jgromes/RadioShield/doc/revC/png/module_CC1101.png

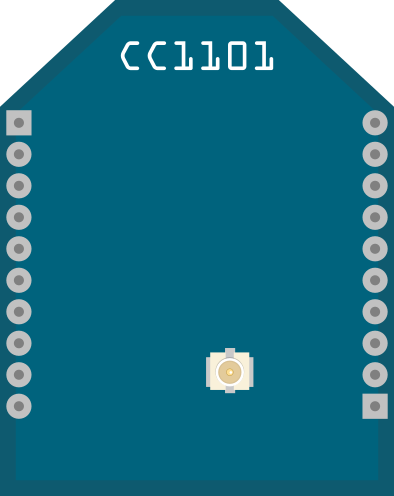
doc/revC/png/module_CC1101.png
