jgromes/RadioShield/doc/revC/png/module_HC05.png

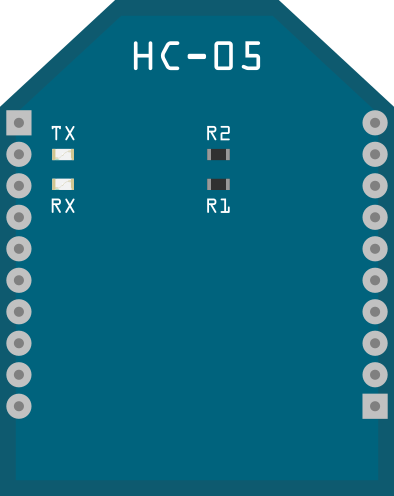
doc/revC/png/module_HC05.png
