jgromes/RadioShield/doc/revC/png/module_SX1272.png

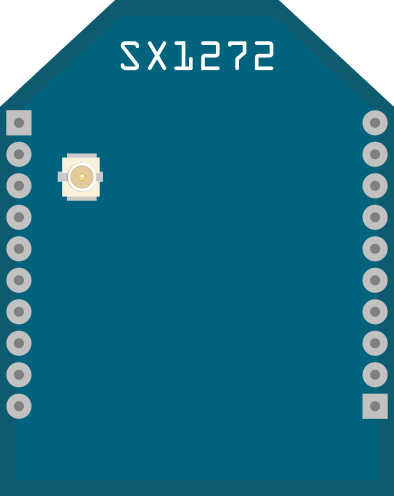
doc/revC/png/module_SX1272.png
