jgromes/RadioShield/eagle/revB/modules/module_ESP07.brd

## EAGLE design eagle/revB/modules/module_ESP07.brd (2018-07-29, an earlier design)

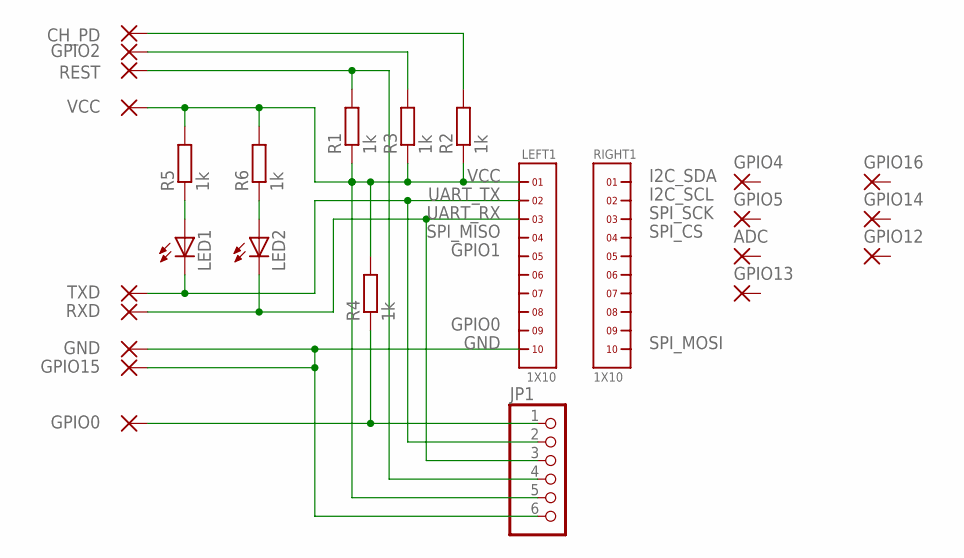
[picture p26: schematic module_ESP07.sch]

Parts:
ADC: WIREPADSMD1,27-254; SMD1,27-2,54
CH_PD: WIREPADSMD1,27-254; SMD1,27-2,54
GND: WIREPADSMD1,27-254; SMD1,27-2,54
GPIO0, GPIO2, GPIO4, GPIO5, GPIO12, GPIO13, GPIO14, GPIO15, GPIO16: WIREPADSMD1,27-254; SMD1,27-2,54
JP1: PINHD-1X6; 1X06
LED1, LED2: LEDCHIPLED_0603; CHIPLED_0603
LEFT1: 1X10
R1, R2, R3, R4, R5, R6: 1k; R0603
REST: WIREPADSMD1,27-254; SMD1,27-2,54
RIGHT1: 1X10
RXD: WIREPADSMD1,27-254; SMD1,27-2,54
TXD: WIREPADSMD1,27-254; SMD1,27-2,54
VCC: WIREPADSMD1,27-254; SMD1,27-2,54

Connections:
GND: GND.1, GPIO15.1, JP1.6, LEFT1.10
GPIO0: GPIO0.1, JP1.1, R4.1
unnamed: GPIO2.1, R3.2
unnamed: CH_PD.1, R2.2
unnamed: LED2.A, R6.1
unnamed: LED1.A, R5.1
RST: JP1.4, R1.2, REST.1
UART_RX: JP1.3, LED2.C, LEFT1.3, RXD.1
UART_TX: JP1.2, LED1.C, LEFT1.2, TXD.1
VCC: JP1.5, LEFT1.1, R1.1, R2.1, R3.1, R4.2, R5.2, R6.2, VCC.1

Notes on the sheet:
VCC
I2C_SDA
I2C_SCL
SPI_SCK
SPI_CS
SPI_MOSI
UART_TX
UART_RX
SPI_MISO
GPIO1
GPIO0
GND

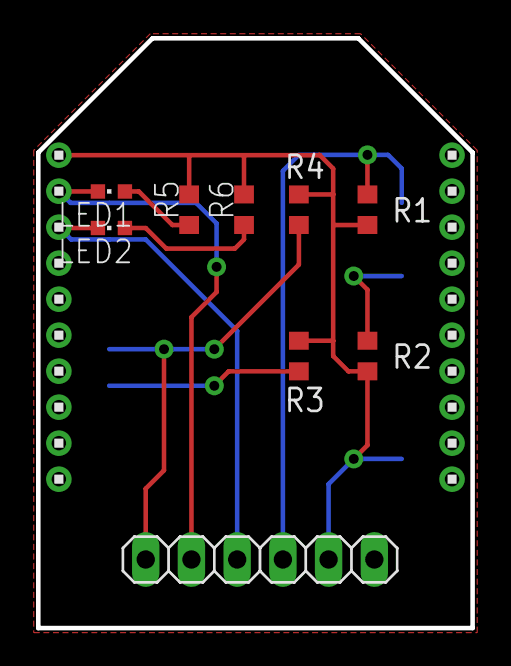
[picture p27: board eagle/revB/modules/module_ESP07.brd from above]

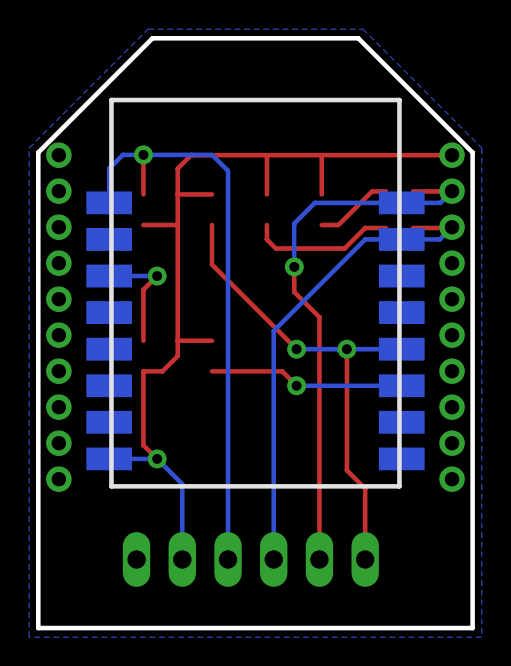
[picture p28: board eagle/revB/modules/module_ESP07.brd from below]

Board: 2 copper layers, 24.1 x 32.8 mm, 27 parts (16 on the bottom side), 10 nets.
