jgromes/RadioShield/eagle/revB/modules/module_HC05.brd

## EAGLE design eagle/revB/modules/module_HC05.brd (2018-07-17, an earlier design)

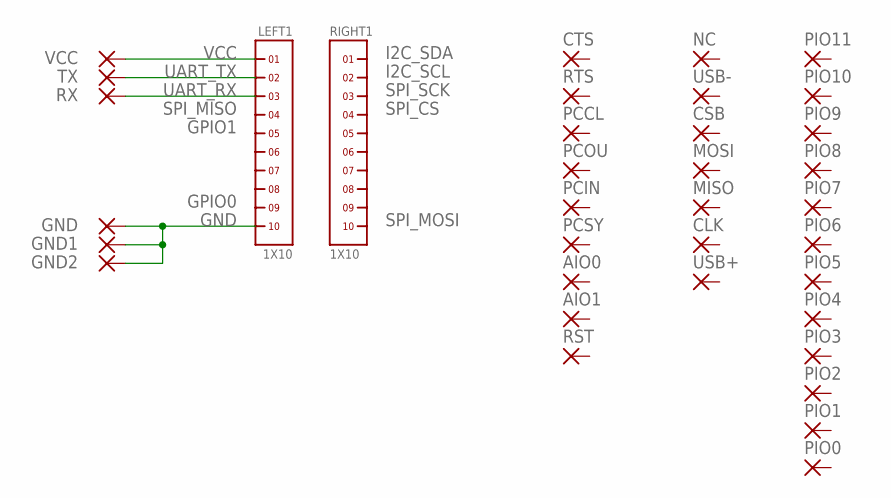
[picture p29: schematic module_HC05.sch]

Parts:
AIO0, AIO1: SMD1; SMD0,65-1,27
CLK: SMD1; SMD0,65-1,27
CSB: SMD1; SMD0,65-1,27
CTS: SMD1; SMD0,65-1,27
GND, GND1, GND2: SMD1; SMD0,65-1,27
LEFT1: 1X10
MISO: SMD1; SMD0,65-1,27
MOSI: SMD1; SMD0,65-1,27
NC: SMD1; SMD0,65-1,27
PCCL: SMD1; SMD0,65-1,27
PCIN: SMD1; SMD0,65-1,27
PCOU: SMD1; SMD0,65-1,27
PCSY: SMD1; SMD0,65-1,27
PIO0, PIO1, PIO2, PIO3, PIO4, PIO5, PIO6, PIO7, PIO8, PIO9, PIO10, PIO11: SMD1; SMD0,65-1,27
RIGHT1: 1X10
RST: SMD1; SMD0,65-1,27
RTS: SMD1; SMD0,65-1,27
RX: SMD1; SMD0,65-1,27
TX: SMD1; SMD0,65-1,27
USB+: SMD1; SMD0,65-1,27
USB-: SMD1; SMD0,65-1,27
VCC: SMD1; SMD0,65-1,27

Connections:
GND: GND.1, GND1.1, GND2.1, LEFT1.10
UART_RX: LEFT1.3, RX.1
UART_TX: LEFT1.2, TX.1
VCC: LEFT1.1, VCC.1

Notes on the sheet:
VCC
I2C_SDA
I2C_SCL
SPI_SCK
SPI_CS
SPI_MOSI
UART_TX
UART_RX
SPI_MISO
GPIO1
GPIO0
GND
