jgromes/RadioShield/eagle/revB/modules/module_HC05.brd

## EAGLE design eagle/revB/modules/module_HC05.brd (continued)

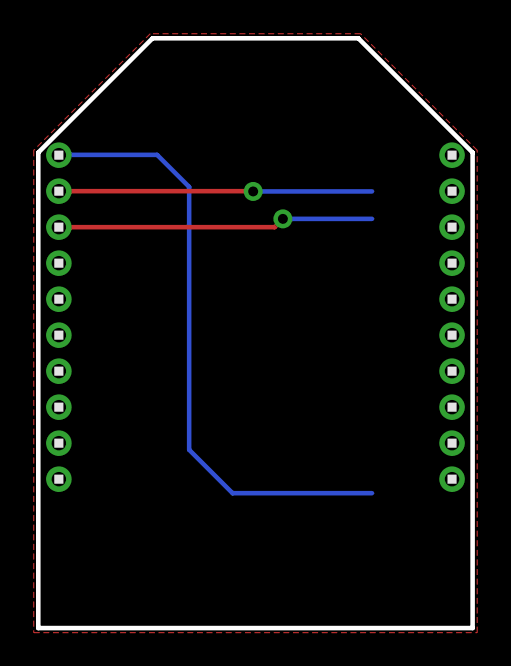
[picture p30: board eagle/revB/modules/module_HC05.brd from above]

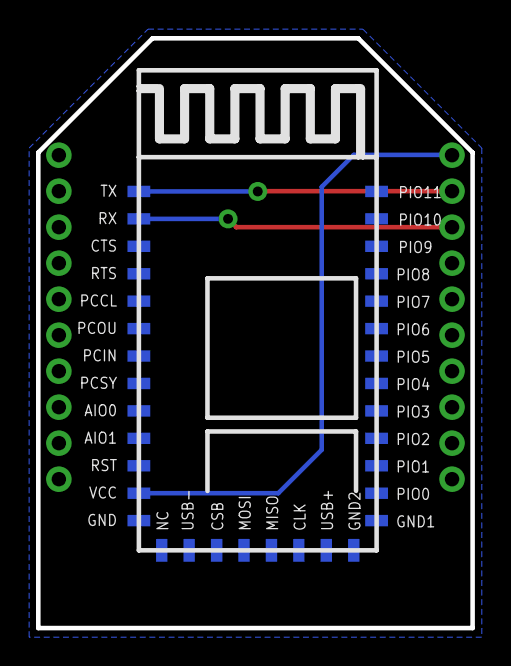
[picture p31: board eagle/revB/modules/module_HC05.brd from below]

Board: 2 copper layers, 24.1 x 32.8 mm, 36 parts (34 on the bottom side), 4 nets.
