jgromes/RadioShield/eagle/revB/shield.brd

## EAGLE design eagle/revB/shield.brd (2018-07-17, an earlier design)

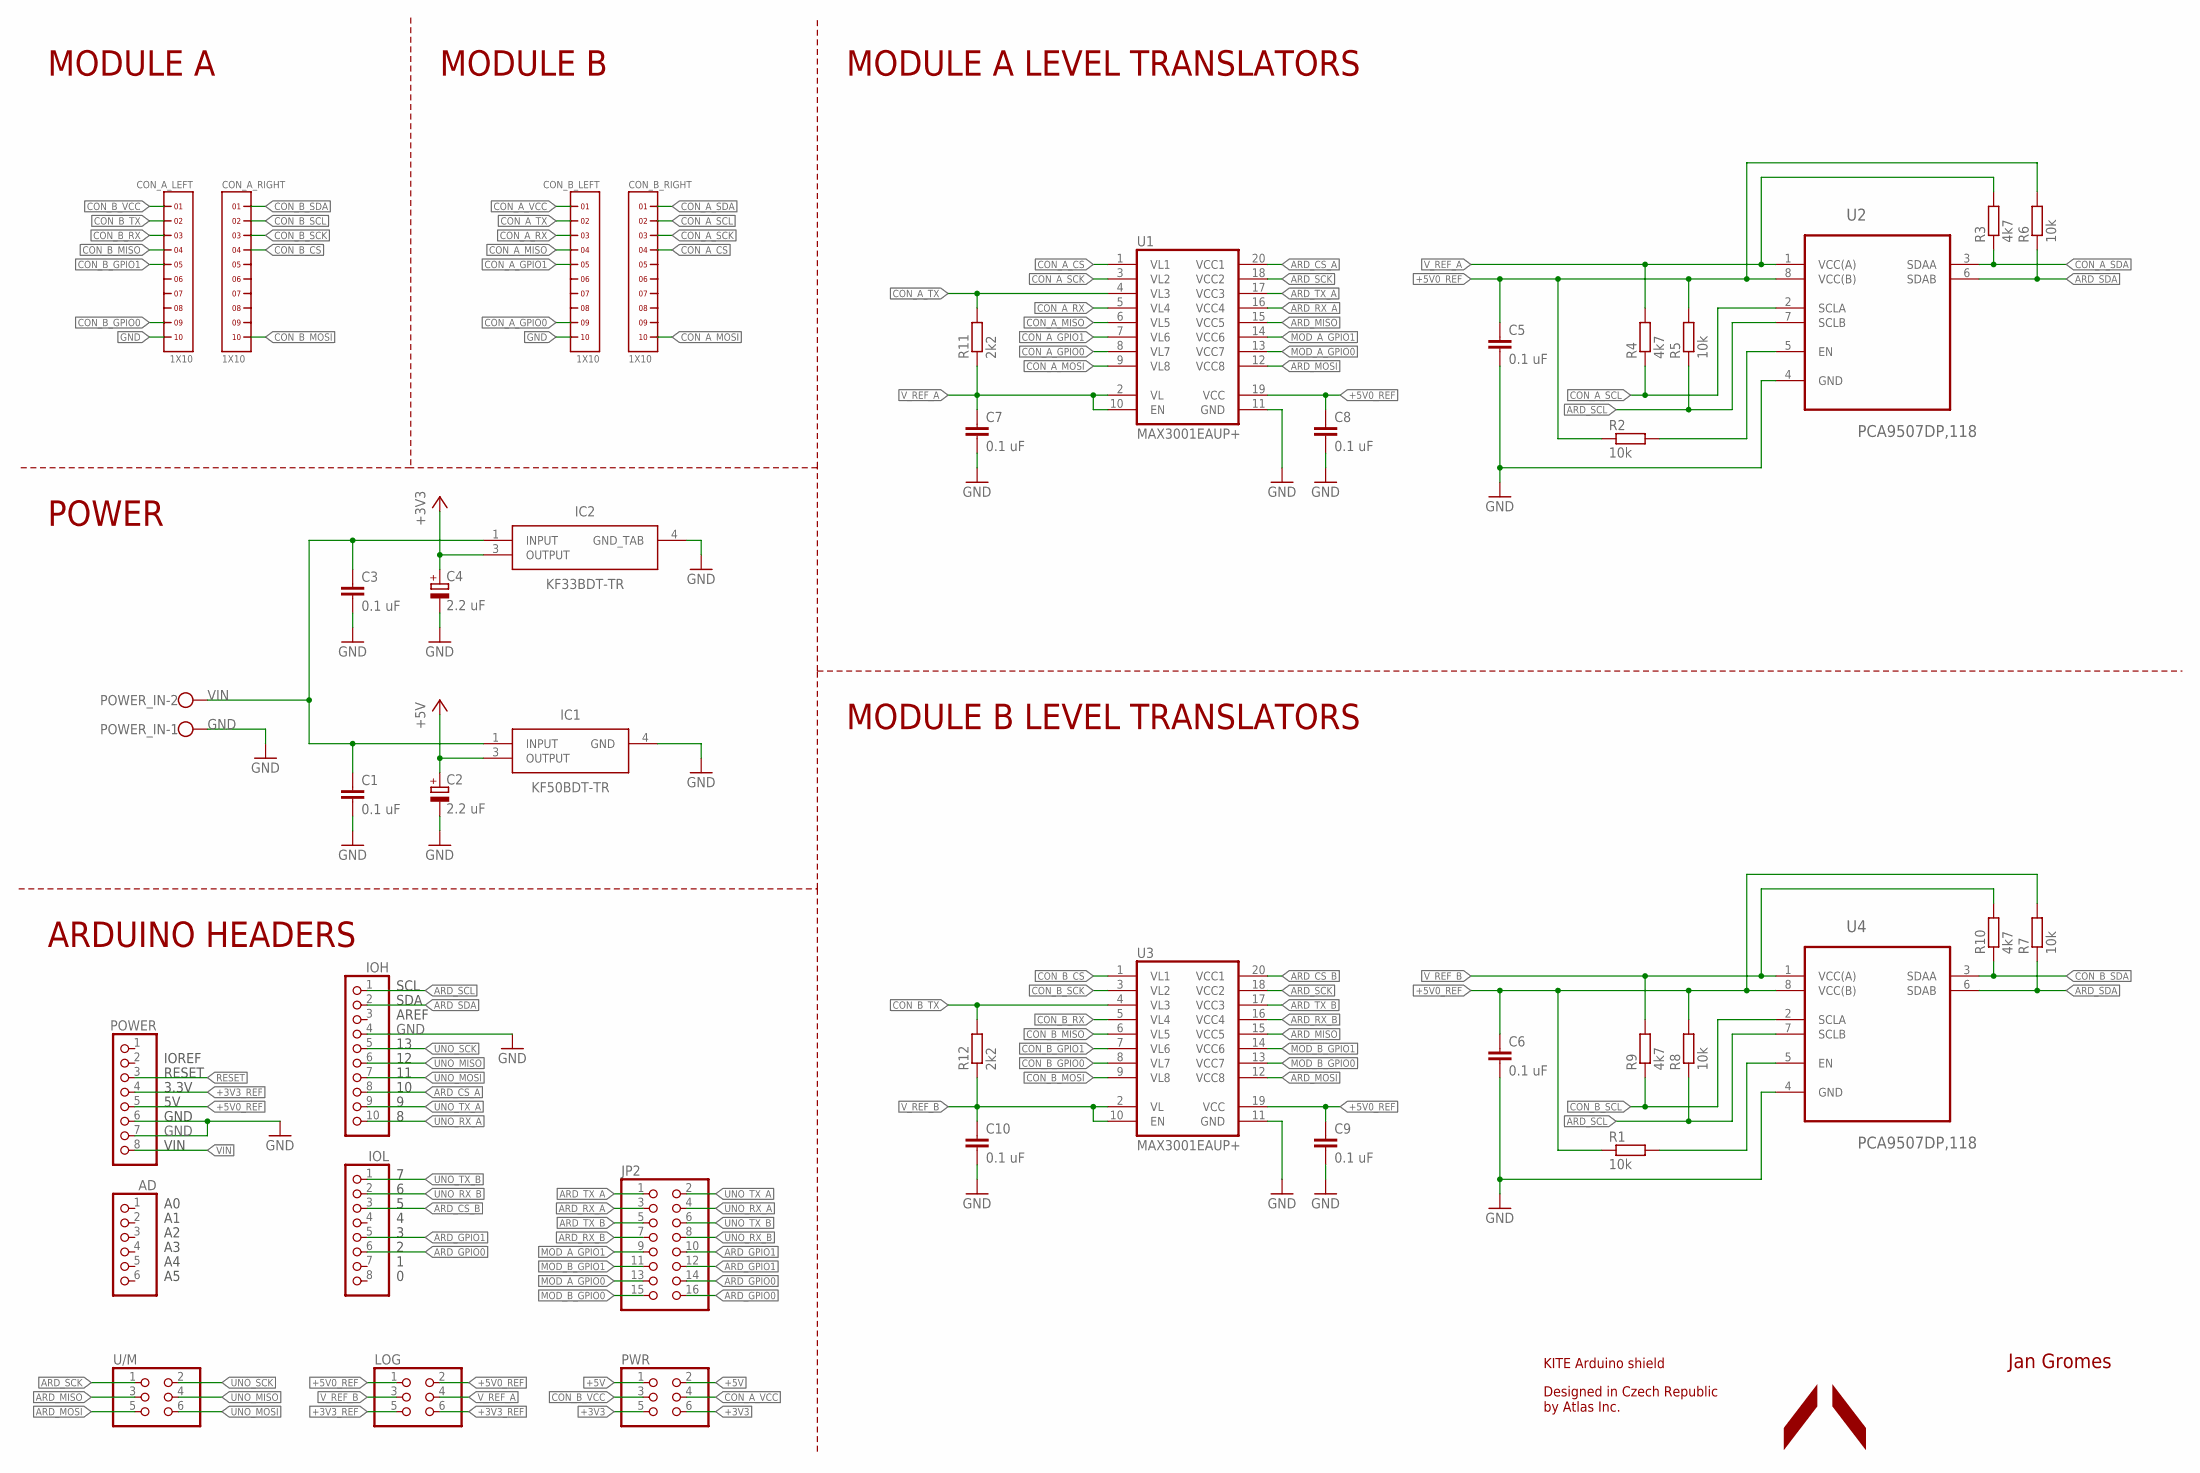
[picture p32: schematic shield.sch, Project WaveLength Arduino shield]

Parts:
AD: PINHD-1X6; 1X06
C1, C3, C5, C6, C7, C8, C9, C10: 0.1 uF; C0603
C2, C4: 2.2 uF; SMC_A
CON_A_LEFT: 1X10
CON_A_RIGHT: 1X10
CON_B_LEFT: 1X10
CON_B_RIGHT: 1X10
IC1: KF50BDT-TR; TO228P972X240-3N
IC2: KF33BDT-TR; TO228P972X240-3N
IOH: PINHD-1X10; 1X10
IOL: PINHD-1X8; 1X08
JP2: PINHD-2X8; 2X08
LOG: PINHD-2X3; 2X03
POWER: PINHD-1X8; 1X08
POWER_IN: W237-102
PWR: PINHD-2X3; 2X03
R1, R2, R5, R6, R7, R8: 10k; R0603
R3, R4, R9, R10: 4k7; R0603
R11, R12: 2k2; R0603
U1, U3: MAX3001EAUP+; TSSOP20
U2, U4: PCA9507DP,118; SOP65P490X110-8N
U/M: PINHD-2X3; 2X03

Connections:
+3V3: C4.+, IC2.3 (OUTPUT), PWR.5, PWR.6
+3V3_REF: LOG.5, LOG.6, POWER.4
+5V: C2.+, IC1.3 (OUTPUT), PWR.1, PWR.2
+5V0_REF: C5.1, C6.1, C8.1, C9.1, LOG.1, LOG.2, POWER.5, R1.1, R2.1, R5.2, R6.2, R7.2, R8.2, U1.19 (VCC), U2.8 (VCC(B)), U3.19 (VCC), U4.8 (VCC(B))
ARD_CS_A: IOH.8, U1.20 (VCC1)
ARD_CS_B: IOL.3, U3.20 (VCC1)
ARD_GPIO0: IOL.6, JP2.14, JP2.16
ARD_GPIO1: IOL.5, JP2.10, JP2.12
ARD_MISO: U1.15 (VCC5), U3.15 (VCC5), U/M.3
ARD_MOSI: U1.12 (VCC8), U3.12 (VCC8), U/M.5
ARD_RX_A: JP2.3, U1.16 (VCC4)
ARD_RX_B: JP2.7, U3.16 (VCC4)
ARD_SCK: U1.18 (VCC2), U3.18 (VCC2), U/M.1
ARD_SCL: IOH.1, R5.1, R8.1, U2.7 (SCLB), U4.7 (SCLB)
ARD_SDA: IOH.2, R6.1, R7.1, U2.6 (SDAB), U4.6 (SDAB)
ARD_TX_A: JP2.1, U1.17 (VCC3)
ARD_TX_B: JP2.5, U3.17 (VCC3)
CON_A_CS: CON_B_RIGHT.4, U1.1 (VL1)
CON_A_GPIO0: CON_B_LEFT.9, U1.8 (VL7)
CON_A_GPIO1: CON_B_LEFT.5, U1.7 (VL6)
CON_A_MISO: CON_B_LEFT.4, U1.6 (VL5)
CON_A_MOSI: CON_B_RIGHT.10, U1.9 (VL8)
CON_A_RX: CON_B_LEFT.3, U1.5 (VL4)
CON_A_SCK: CON_B_RIGHT.3, U1.3 (VL2)
CON_A_SCL: CON_B_RIGHT.2, R4.1, U2.2 (SCLA)
CON_A_SDA: CON_B_RIGHT.1, R3.1, U2.3 (SDAA)
CON_A_TX: CON_B_LEFT.2, R11.2, U1.4 (VL3)
CON_A_VCC: CON_B_LEFT.1, PWR.4
CON_B_CS: CON_A_RIGHT.4, U3.1 (VL1)
CON_B_GPIO0: CON_A_LEFT.9, U3.8 (VL7)
CON_B_GPIO1: CON_A_LEFT.5, U3.7 (VL6)
CON_B_MISO: CON_A_LEFT.4, U3.6 (VL5)
CON_B_MOSI: CON_A_RIGHT.10, U3.9 (VL8)
CON_B_RX: CON_A_LEFT.3, U3.5 (VL4)
CON_B_SCK: CON_A_RIGHT.3, U3.3 (VL2)
CON_B_SCL: CON_A_RIGHT.2, R9.1, U4.2 (SCLA)
CON_B_SDA: CON_A_RIGHT.1, R10.1, U4.3 (SDAA)
CON_B_TX: CON_A_LEFT.2, R12.2, U3.4 (VL3)
CON_B_VCC: CON_A_LEFT.1, PWR.3
GND: C1.2, C2.-, C3.2, C4.-, C5.2, C6.2, C7.2, C8.2, C9.2, C10.2, CON_A_LEFT.10, CON_B_LEFT.10, IC1.4 (GND), IC2.4 (GND_TAB), IOH.4, POWER.6, POWER.7, POWER_IN.1, U1.11 (GND), U2.4 (GND), U3.11 (GND), U4.4 (GND)
MOD_A_GPIO0: JP2.13, U1.13 (VCC7)
MOD_A_GPIO1: JP2.9, U1.14 (VCC6)
MOD_B_GPIO0: JP2.15, U3.13 (VCC7)
MOD_B_GPIO1: JP2.11, U3.14 (VCC6)
unnamed: R2.2, U2.5 (EN)
unnamed: R1.2, U4.5 (EN)
RESET: POWER.3
UNO_MISO: IOH.6, U/M.4
UNO_MOSI: IOH.7, U/M.6
UNO_RX_A: IOH.10, JP2.4
UNO_RX_B: IOL.2, JP2.8
UNO_SCK: IOH.5, U/M.2
UNO_TX_A: IOH.9, JP2.2
UNO_TX_B: IOL.1, JP2.6
VIN: C1.1, C3.1, IC1.1 (INPUT), IC2.1 (INPUT), POWER.8, POWER_IN.2
V_REF_A: C7.1, LOG.4, R3.2, R4.2, R11.1, U1.2 (VL), U1.10 (EN), U2.1 (VCC(A))
V_REF_B: C10.1, LOG.3, R9.2, R10.2, R12.1, U3.2 (VL), U3.10 (EN), U4.1 (VCC(A))

Notes on the sheet:
Jan Gromes
AREF
SDA
SCL
VIN
GND
3.3V
RESET
IOREF
MODULE B LEVEL TRANSLATORS
MODULE A LEVEL TRANSLATORS
MODULE A
MODULE B
POWER
ARDUINO HEADERS
KITE Arduino shield
Designed in Czech Republic by Atlas Inc.

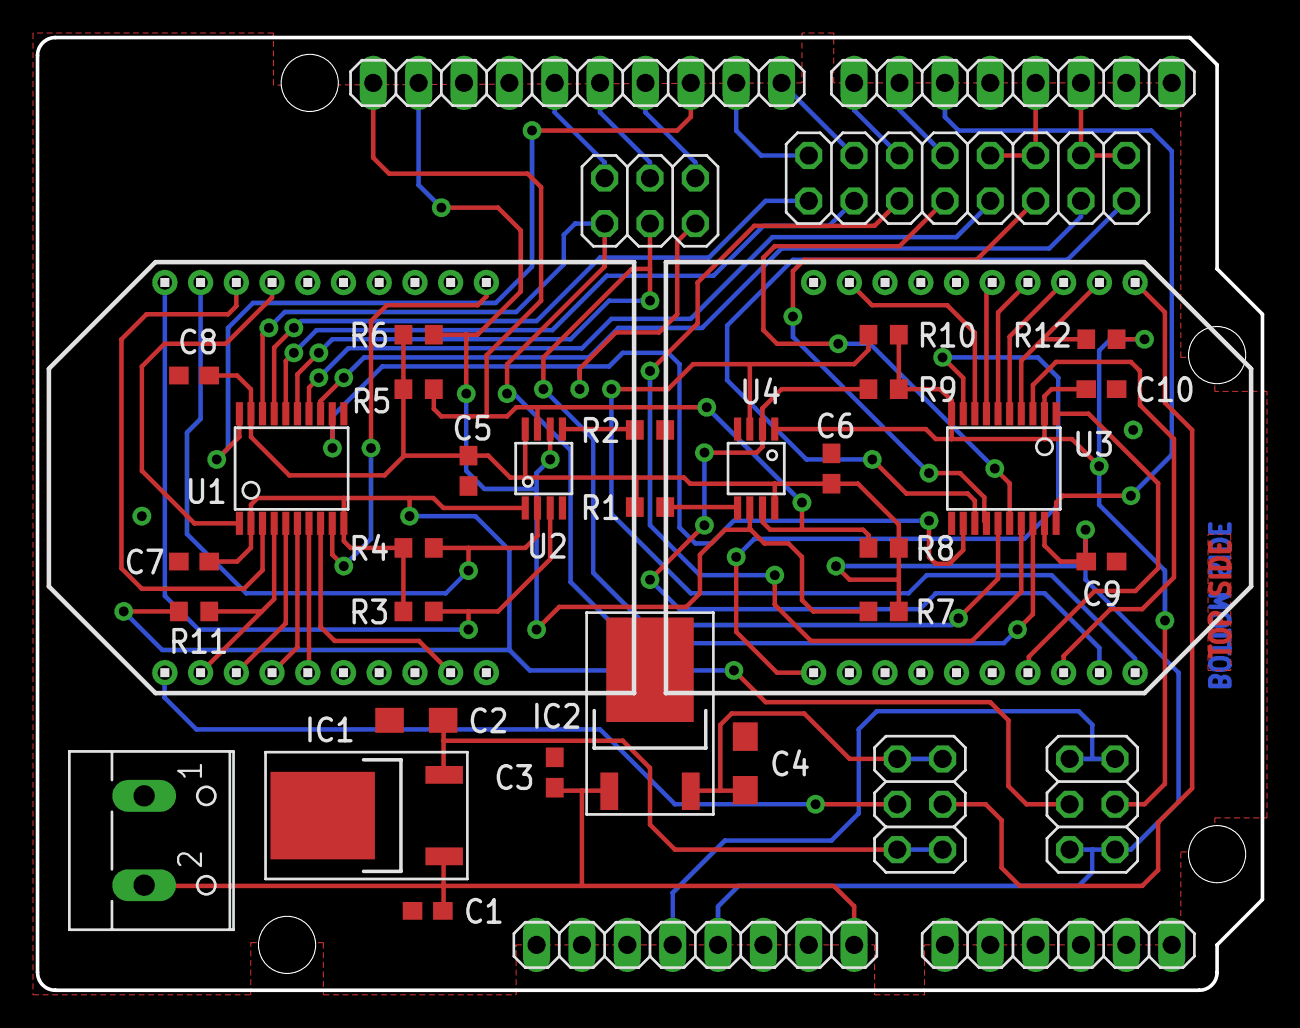
[picture p33: board eagle/revB/shield.brd from above]

Board: 2 copper layers, 68.6 x 53.3 mm, 41 parts (0 on the bottom side), 56 nets.
