jgromes/RadioShield/eagle/revB/modules/module_RF69.brd

## EAGLE design eagle/revB/modules/module_RF69.brd (2018-07-20, an earlier design)

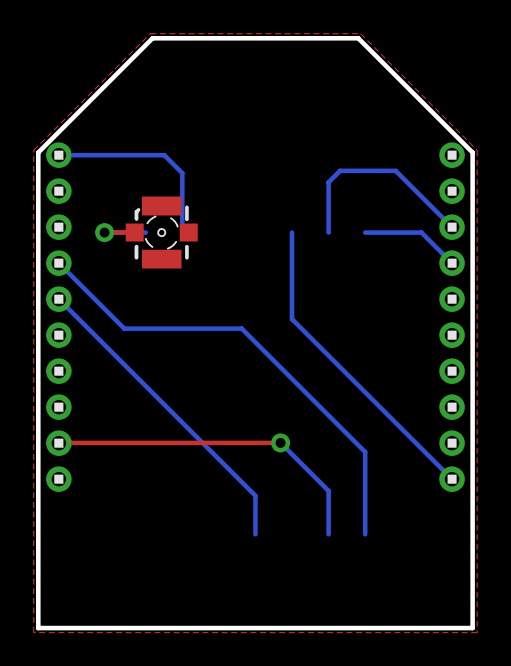
[picture p34: board module_RF69.brd from above]

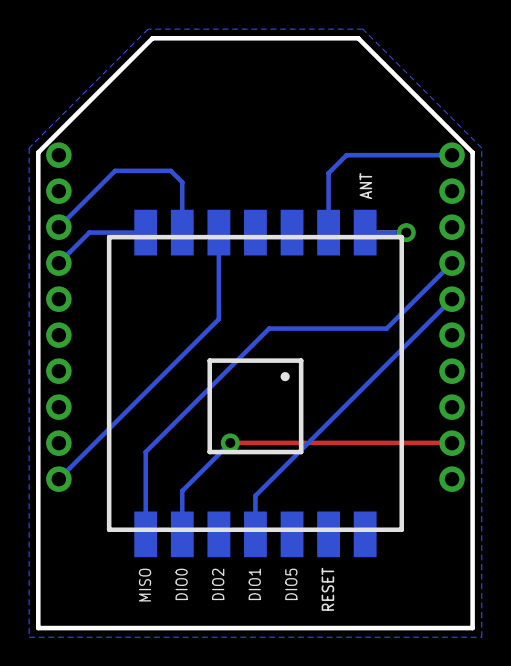
[picture p35: board module_RF69.brd from below]

Board: 2 copper layers, 24.1 x 32.8 mm, 17 parts (14 on the bottom side), 9 nets.

Parts:
3.3V: SMD1,27-2,54
ANT: SMD1,27-2,54
DIO0, DIO1, DIO2, DIO3, DIO5: SMD1,27-2,54
GND: SMD1,27-2,54
GND_ANT: SMD1,27-2,54
LEFT1: 1X10
MISO: SMD1,27-2,54
MOSI: SMD1,27-2,54
NSS: SMD1,27-2,54
RESET: SMD1,27-2,54
RIGHT1: 1X10
SCK: SMD1,27-2,54
X1: 734120110

Connections:
ANT: ANT.1, X1.1
GND: GND.1, GND_ANT.1, LEFT1.10, X1.S@1, X1.S@2, X1.S@3
INT0: DIO0.1, LEFT1.9
INT1: DIO1.1, LEFT1.5
SPI_CS: NSS.1, RIGHT1.4
SPI_MISO: LEFT1.4, MISO.1
SPI_MOSI: MOSI.1, RIGHT1.10
SPI_SCK: RIGHT1.3, SCK.1
VCC: 3.3V.1, LEFT1.1
