jgromes/RadioShield/eagle/revB/modules/module_JDY08.brd

## EAGLE design eagle/revB/modules/module_JDY08.brd (2018-07-17, an earlier design)

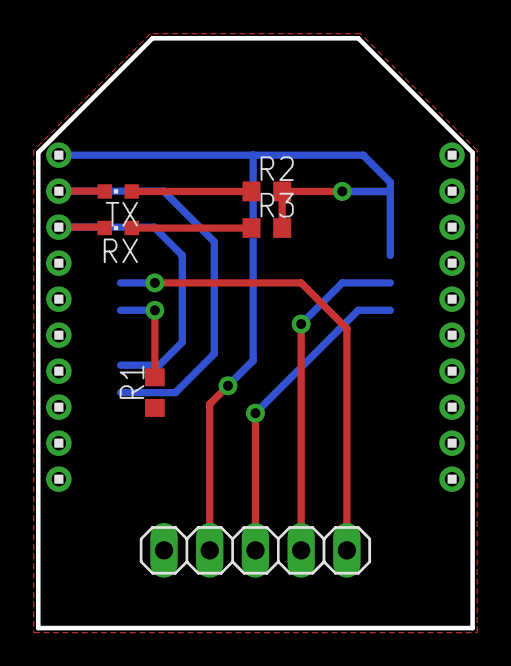
[picture p36: board eagle/revB/modules/module_JDY08.brd from above]

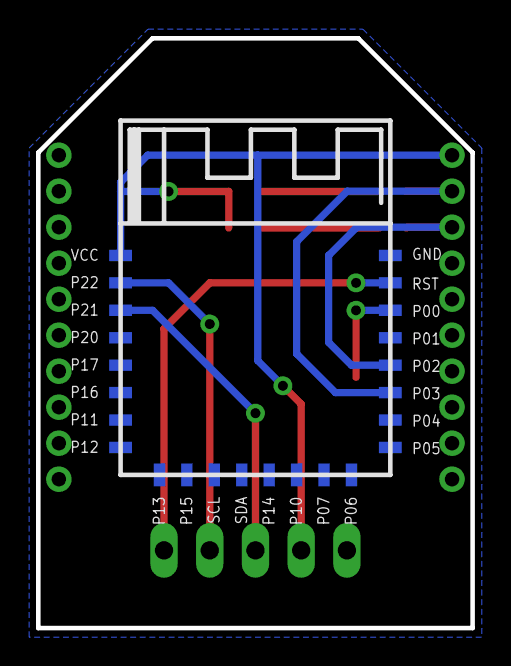
[picture p37: board eagle/revB/modules/module_JDY08.brd from below]

Board: 2 copper layers, 24.1 x 32.8 mm, 32 parts (24 on the bottom side), 10 nets.

Parts:
GND: SMD0,65-1,27
JP1: 1X05
LEFT1: 1X10
P00, P01, P02, P03, P04, P05, P06, P07, P10, P11, P12, P13, P14, P15, P16, P17, P20, P21, P22: SMD0,65-1,27
R1, R2, R3: 1K; R0603
RIGHT1: 1X10
RST: SMD0,65-1,27
RX: CHIPLED_0603
SCL: SMD0,65-1,27
SDA: SMD0,65-1,27
TX: CHIPLED_0603
VCC: SMD0,65-1,27

Connections:
GND: GND.1, JP1.1, LEFT1.10, R1.1
unnamed: JP1.5, RST.1
unnamed: JP1.3, P21.1
unnamed: JP1.4, P22.1
unnamed: P00.1, R1.2
unnamed: LEFT1.3, P02.1, RX.C
unnamed: LEFT1.2, P03.1, TX.C
unnamed: R2.1, TX.A
unnamed: R3.1, RX.A
VCC: JP1.2, LEFT1.1, R2.2, R3.2, VCC.1
